fchorney/krakenpad-poc/review/01-master/02-2d-top.png

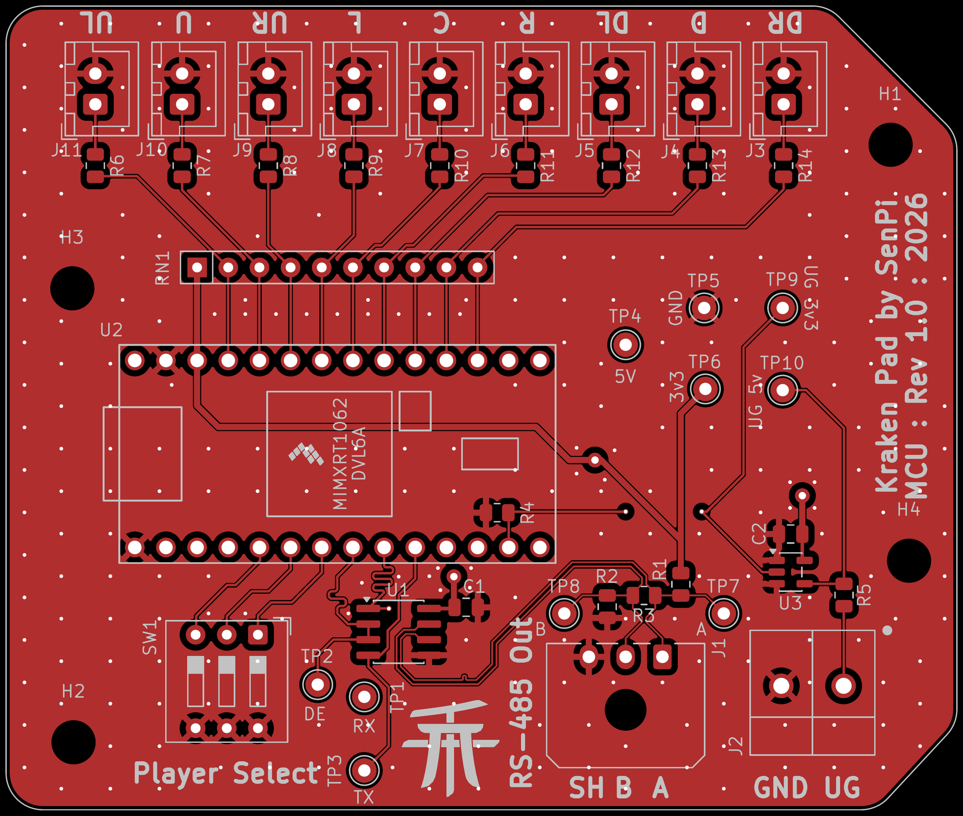
review/01-master/02-2d-top.png
