fchorney/krakenpad-poc/review/01-master/03-2d-in1.png

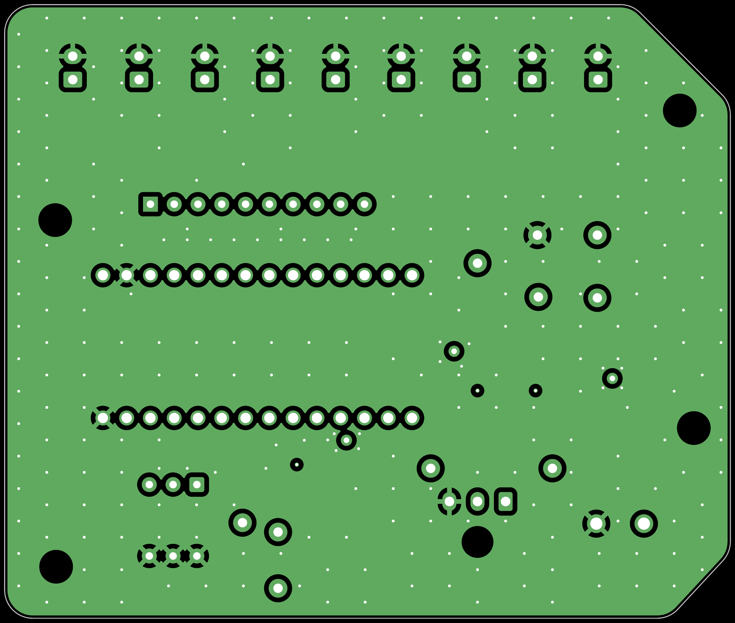
review/01-master/03-2d-in1.png
