fchorney/krakenpad-poc/review/01-master/05-2d-bottom-mirrored.png

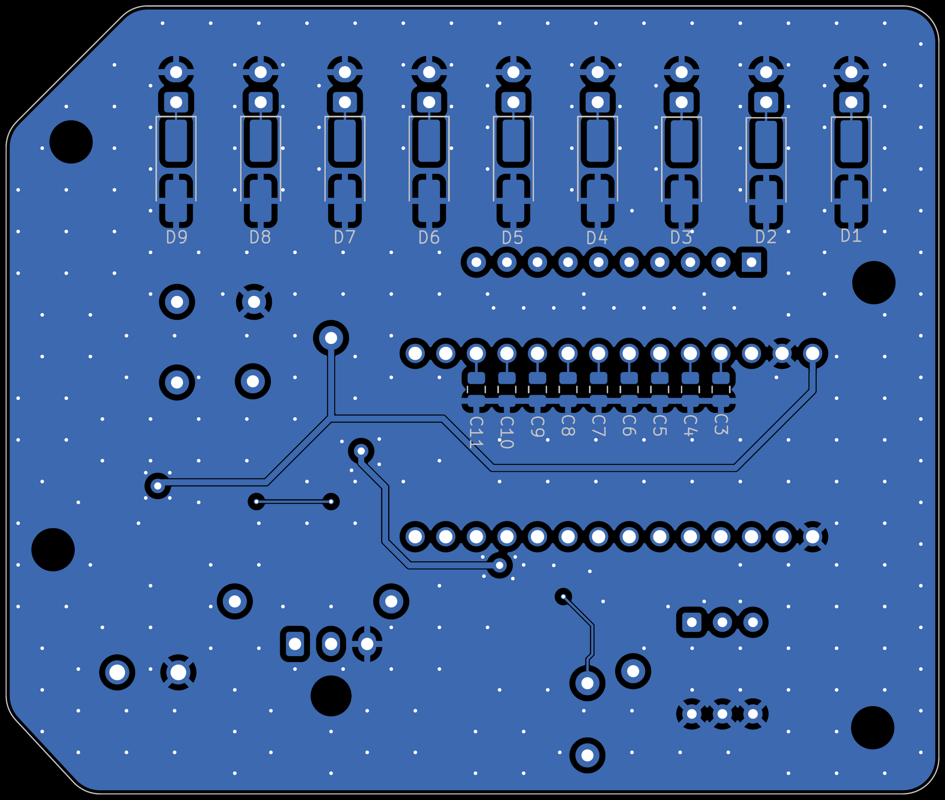
review/01-master/05-2d-bottom-mirrored.png
