fchorney/krakenpad-poc/review/01-master/06-2d-silkscreen-top.png

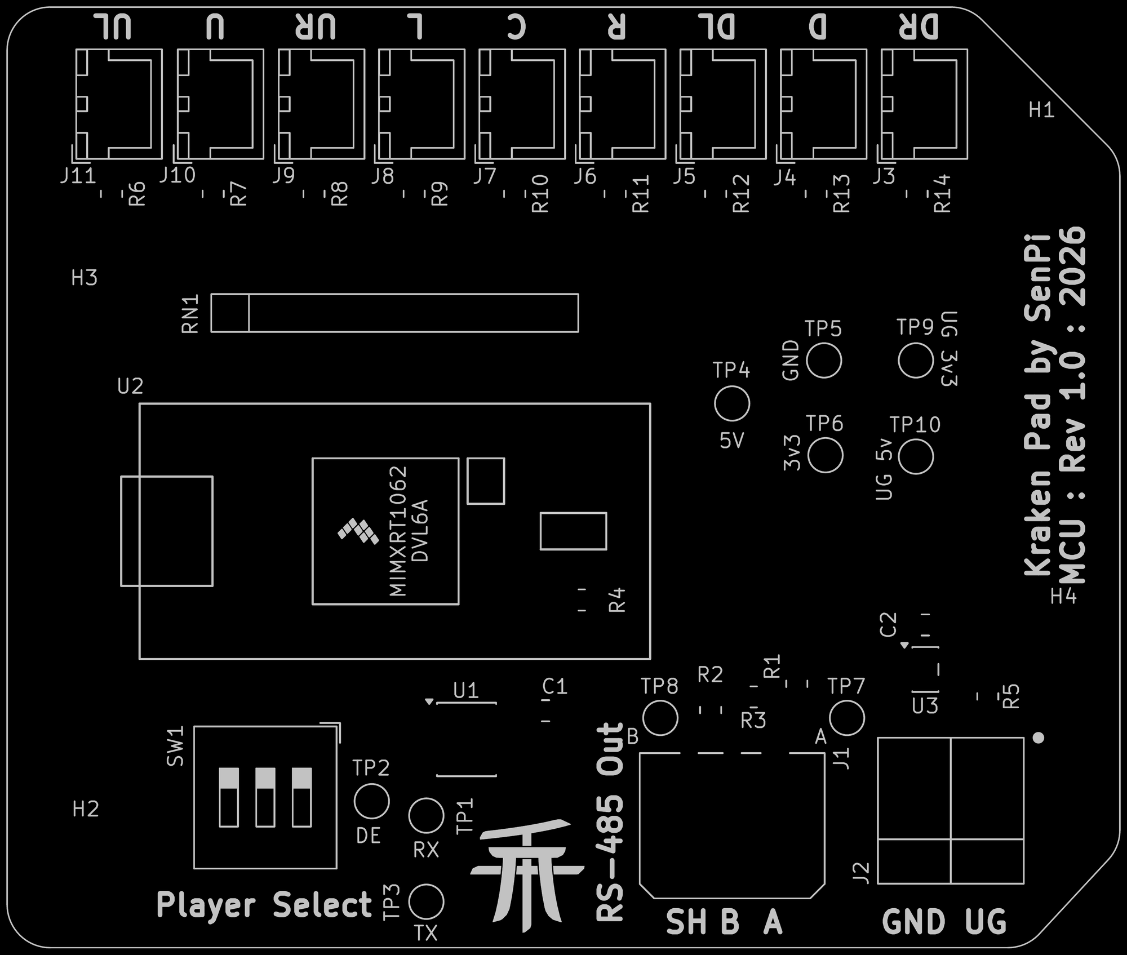
review/01-master/06-2d-silkscreen-top.png
