fchorney/krakenpad-poc/review/01-master/07-2d-top-no-pour.png

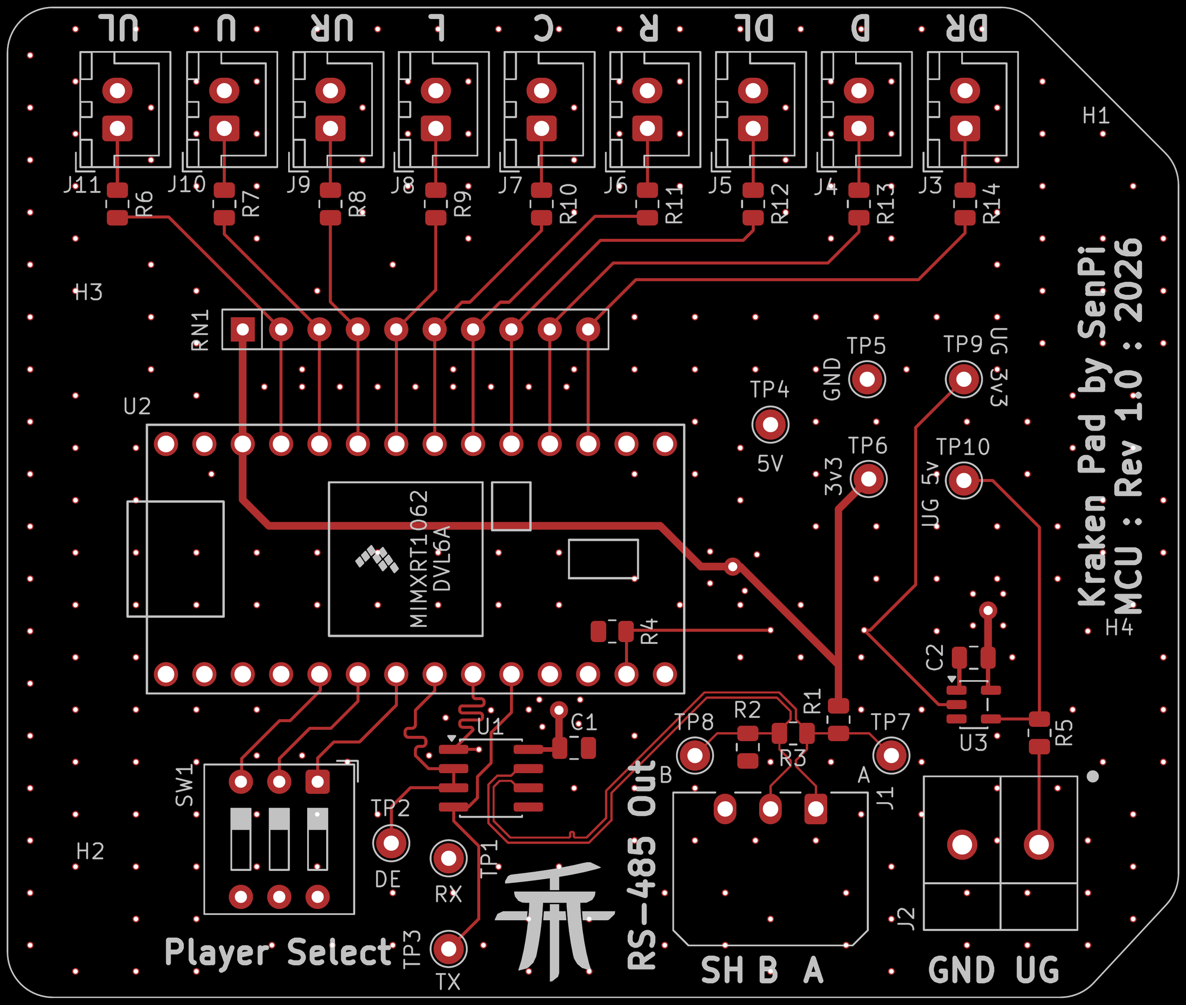
review/01-master/07-2d-top-no-pour.png
