fchorney/krakenpad-poc/review/01-master/08-2d-in1-no-pour.png

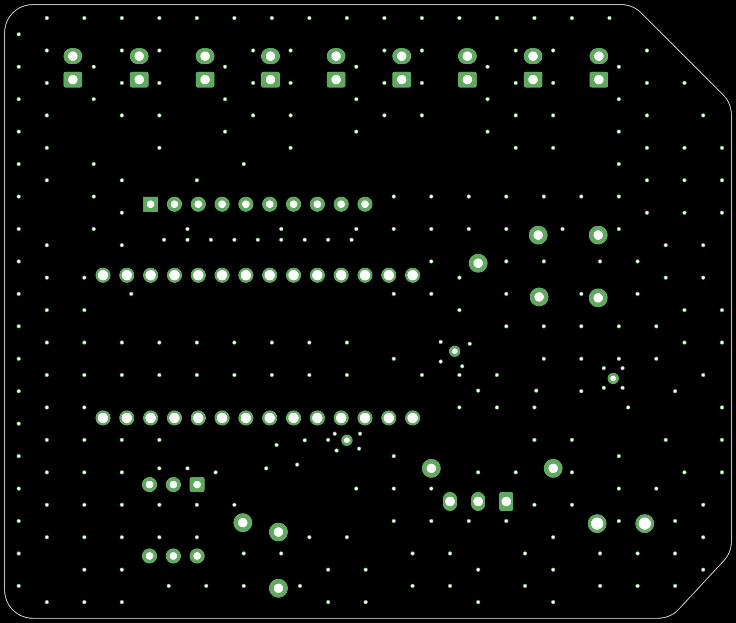
review/01-master/08-2d-in1-no-pour.png
