fchorney/krakenpad-poc/review/01-master/10-2d-bottom-no-pour-mirrored.png

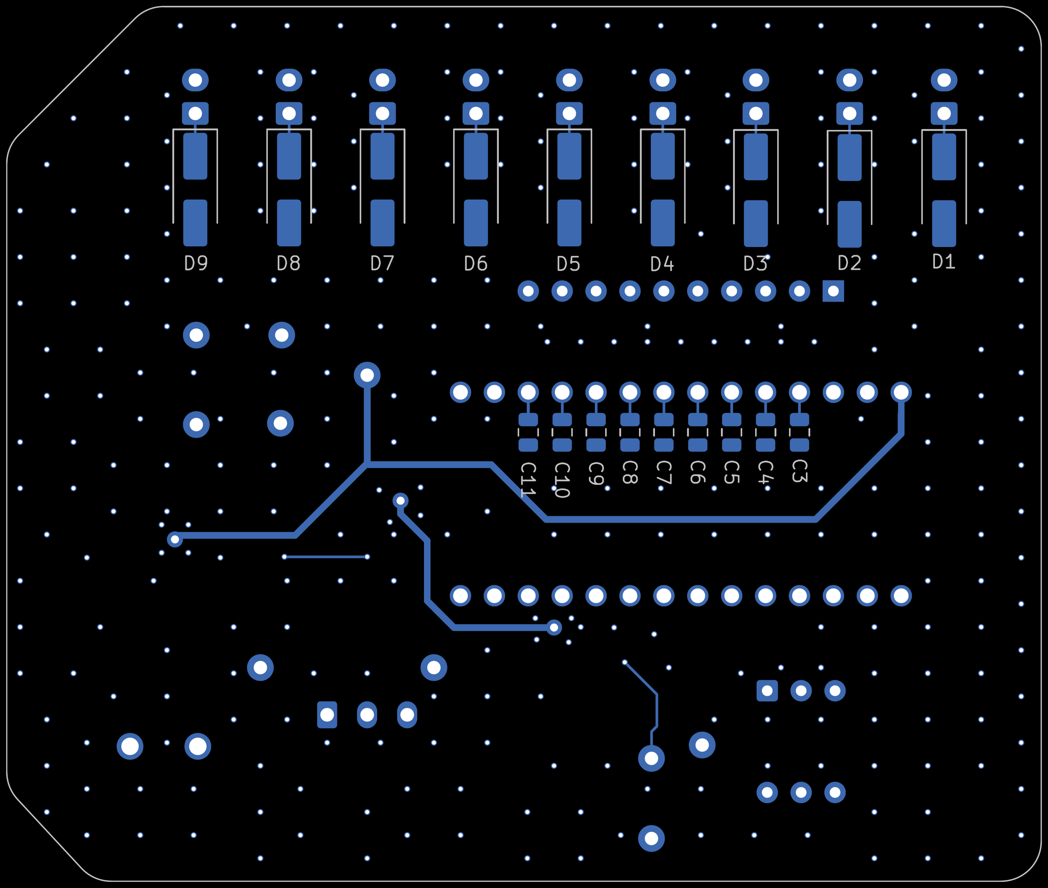
review/01-master/10-2d-bottom-no-pour-mirrored.png
