fchorney/krakenpad-poc/review/01-master/12-3d-bottom.png

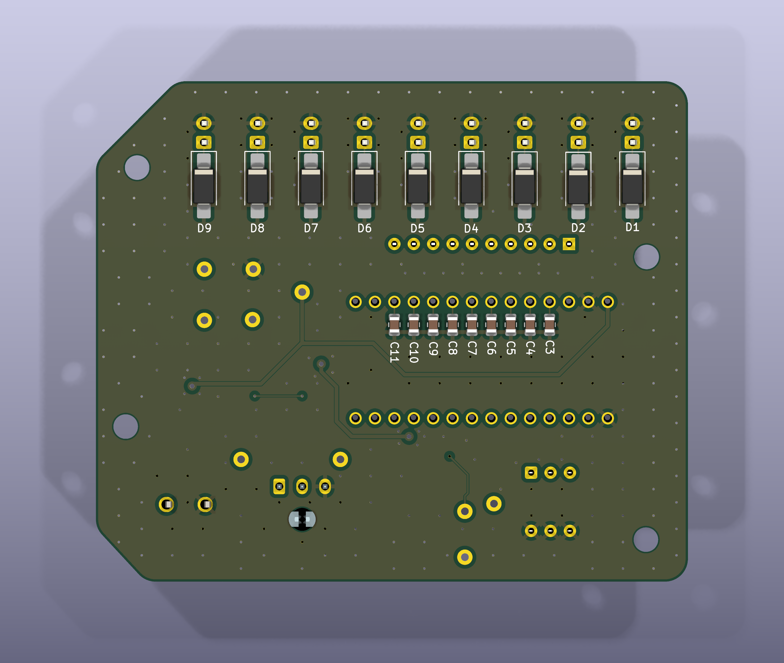
review/01-master/12-3d-bottom.png
