fchorney/krakenpad-poc/review/03-dual-carrier/02-2d-top.png

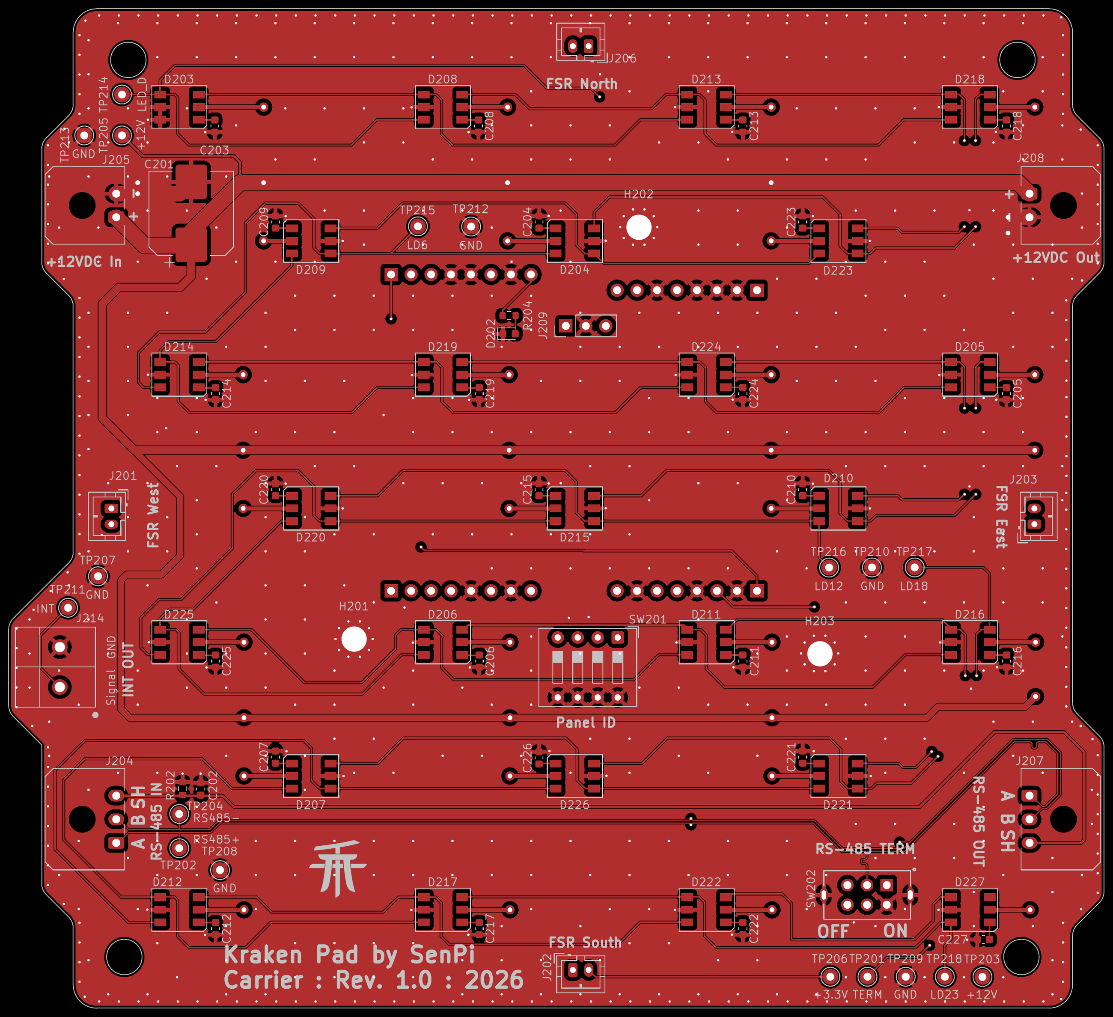
review/03-dual-carrier/02-2d-top.png
