fchorney/krakenpad-poc/review/03-dual-carrier/03-2d-in1.png

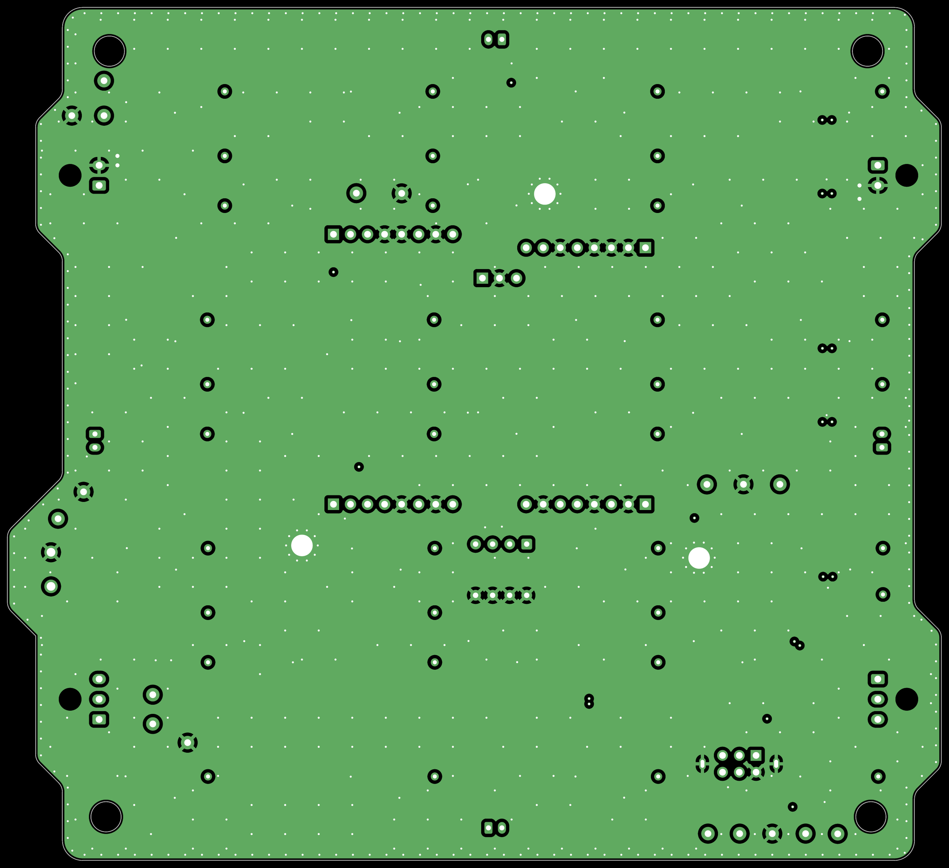
review/03-dual-carrier/03-2d-in1.png
