fchorney/krakenpad-poc/review/03-dual-carrier/05-2d-bottom-mirrored.png

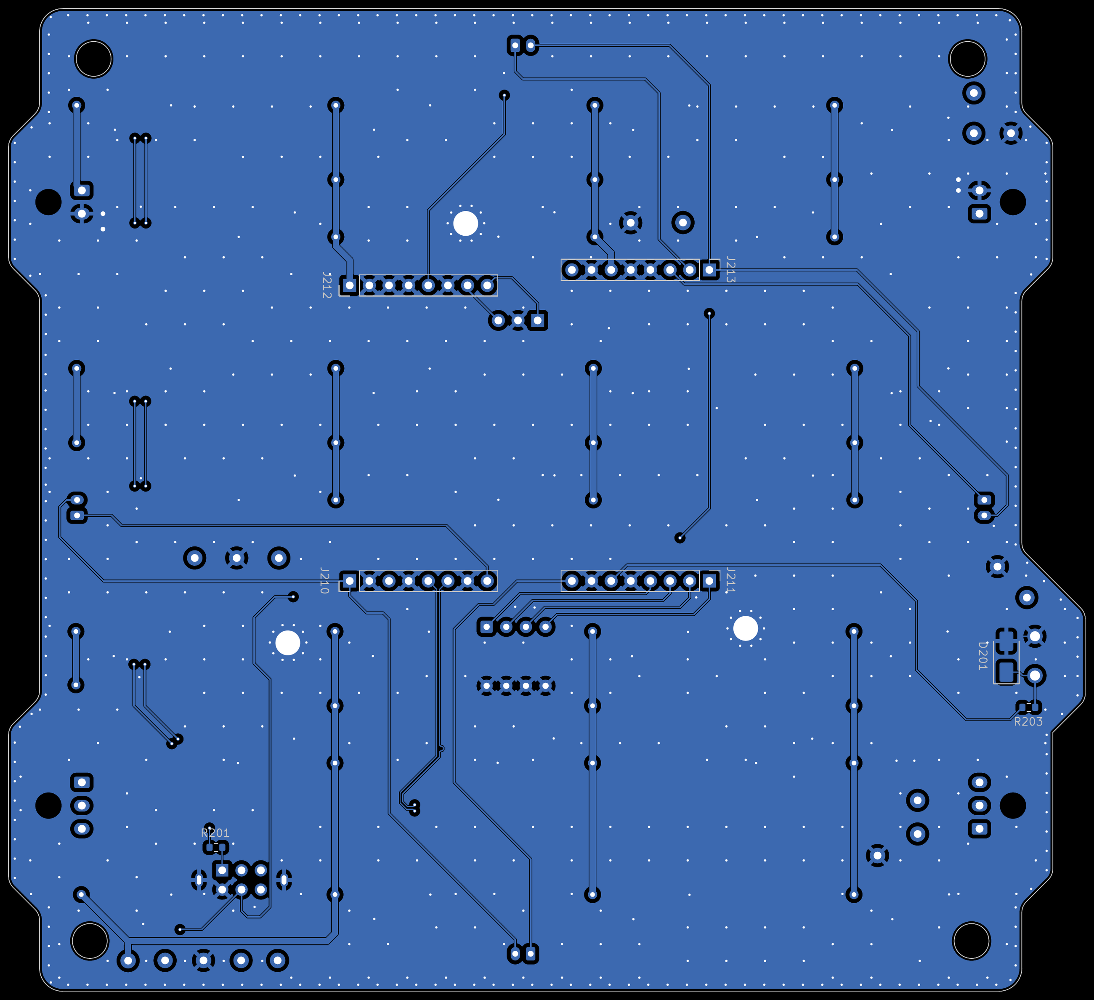
review/03-dual-carrier/05-2d-bottom-mirrored.png
