fchorney/krakenpad-poc/review/03-dual-carrier/06-2d-silkscreen-top.png

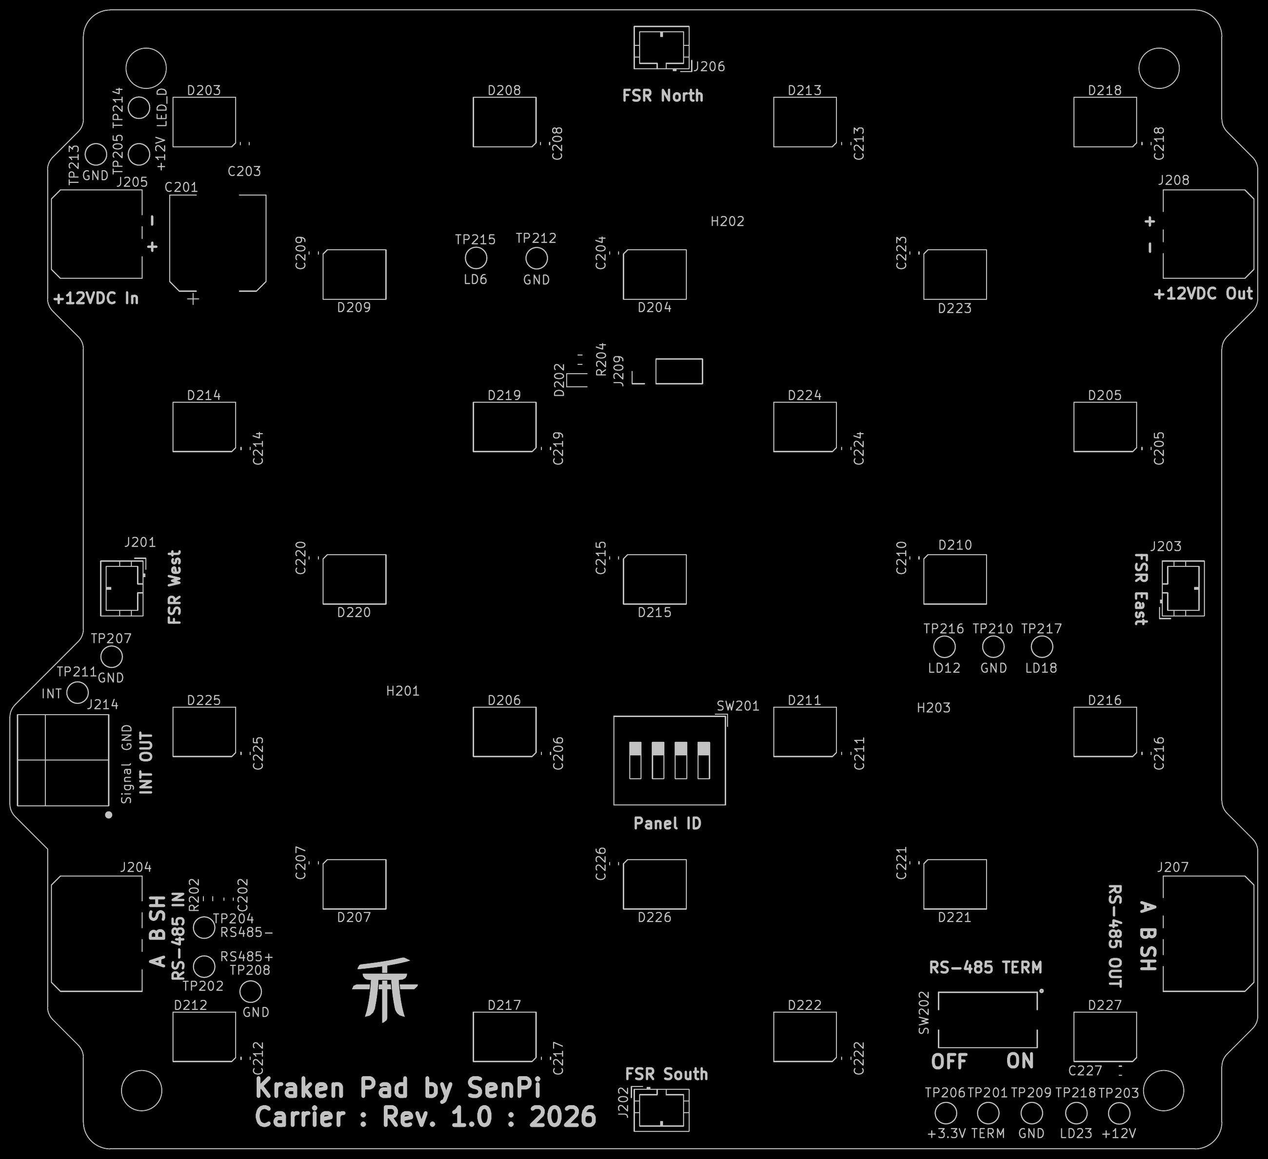
review/03-dual-carrier/06-2d-silkscreen-top.png
