fchorney/krakenpad-poc/review/03-dual-carrier/07-2d-top-no-pour.png

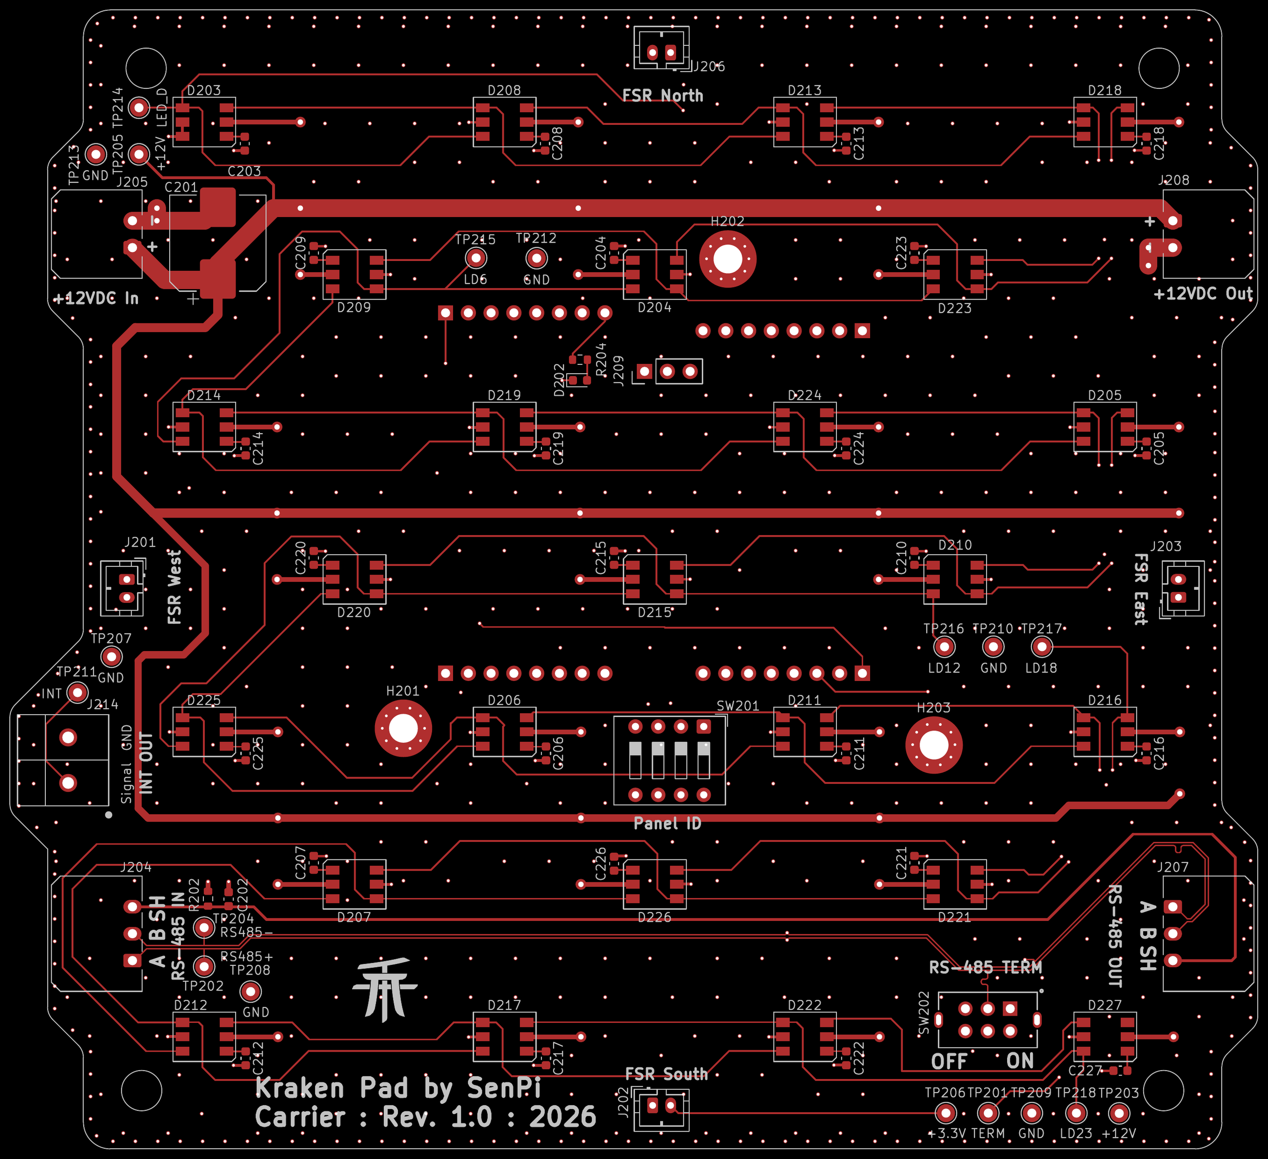
review/03-dual-carrier/07-2d-top-no-pour.png
