fchorney/krakenpad-poc/review/03-dual-carrier/08-2d-in1-no-pour.png

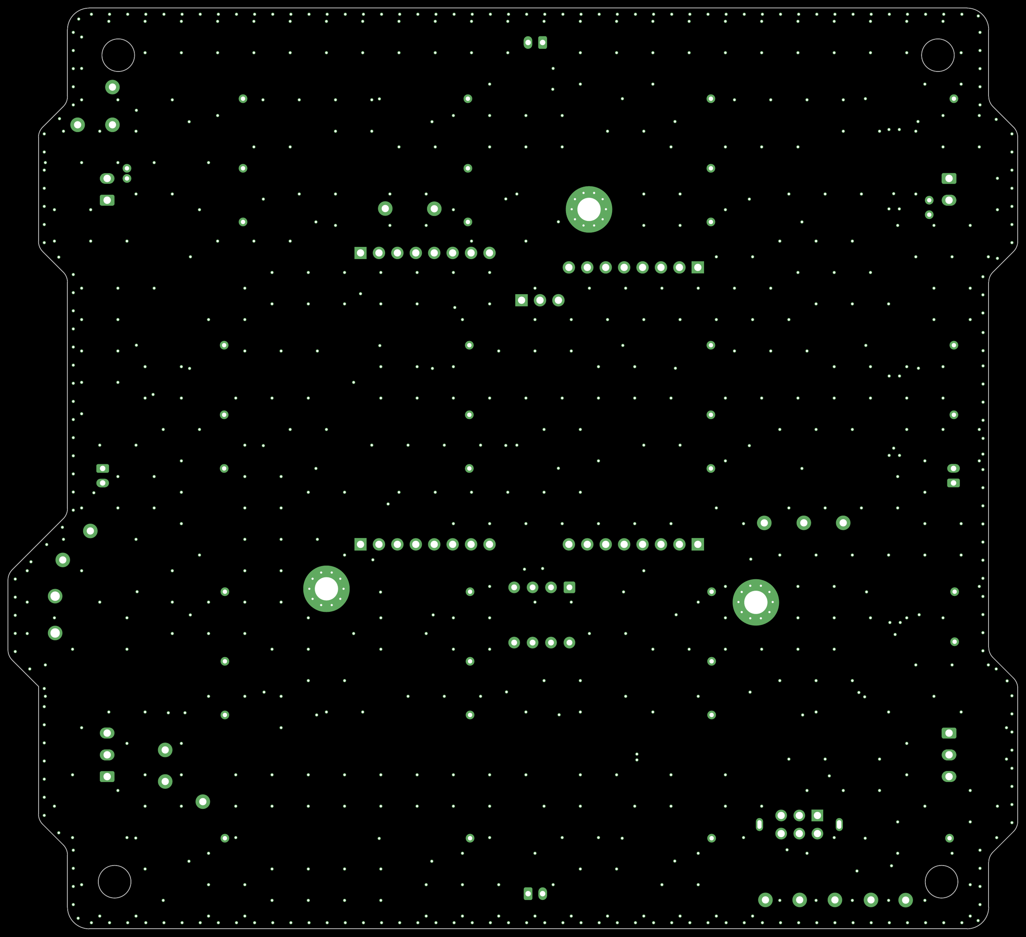
review/03-dual-carrier/08-2d-in1-no-pour.png
