fchorney/krakenpad-poc/review/03-dual-carrier/10-2d-bottom-no-pour-mirrored.png

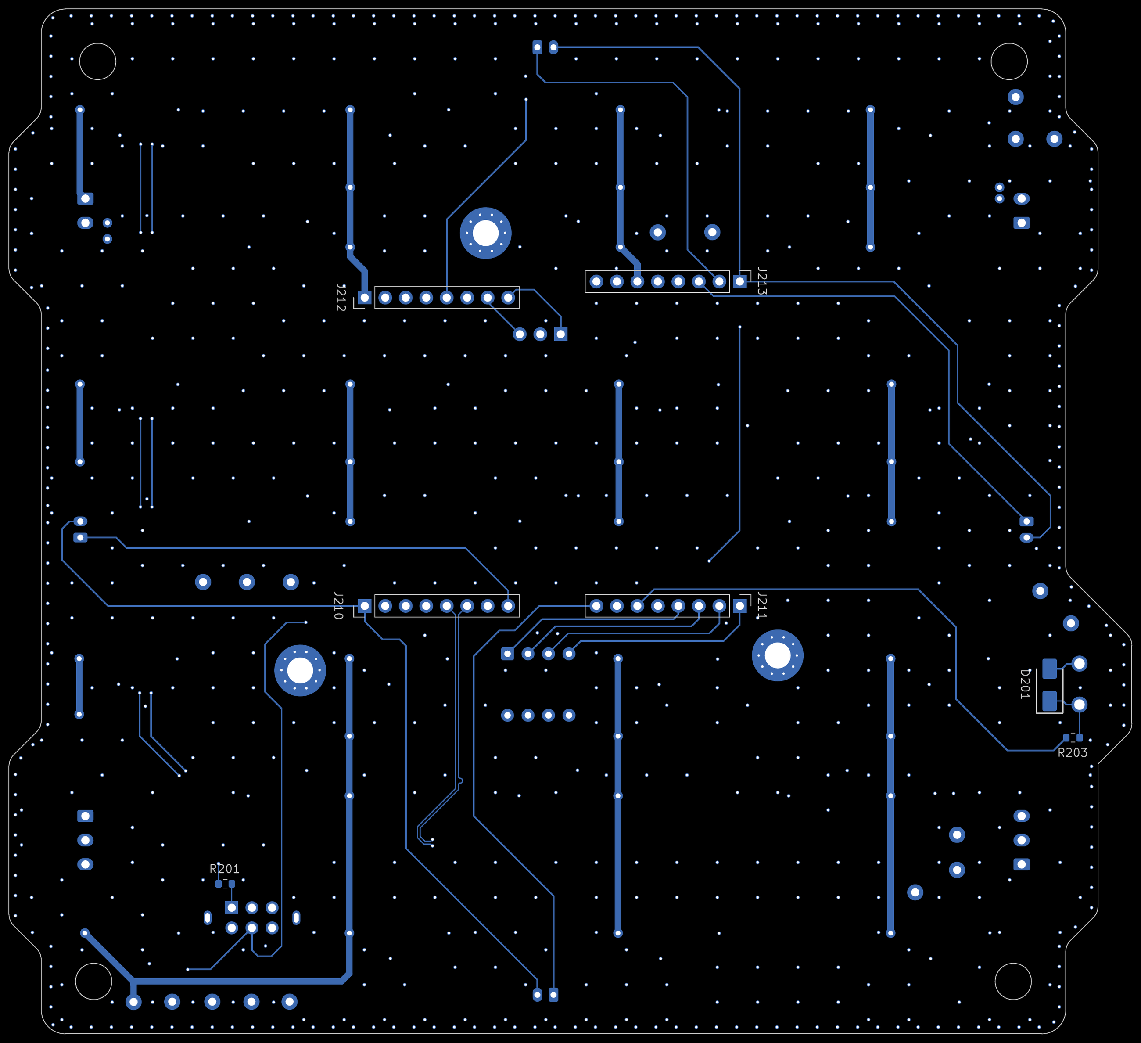
review/03-dual-carrier/10-2d-bottom-no-pour-mirrored.png
