fchorney/krakenpad-poc/review/03-dual-carrier/11-3d-top.png

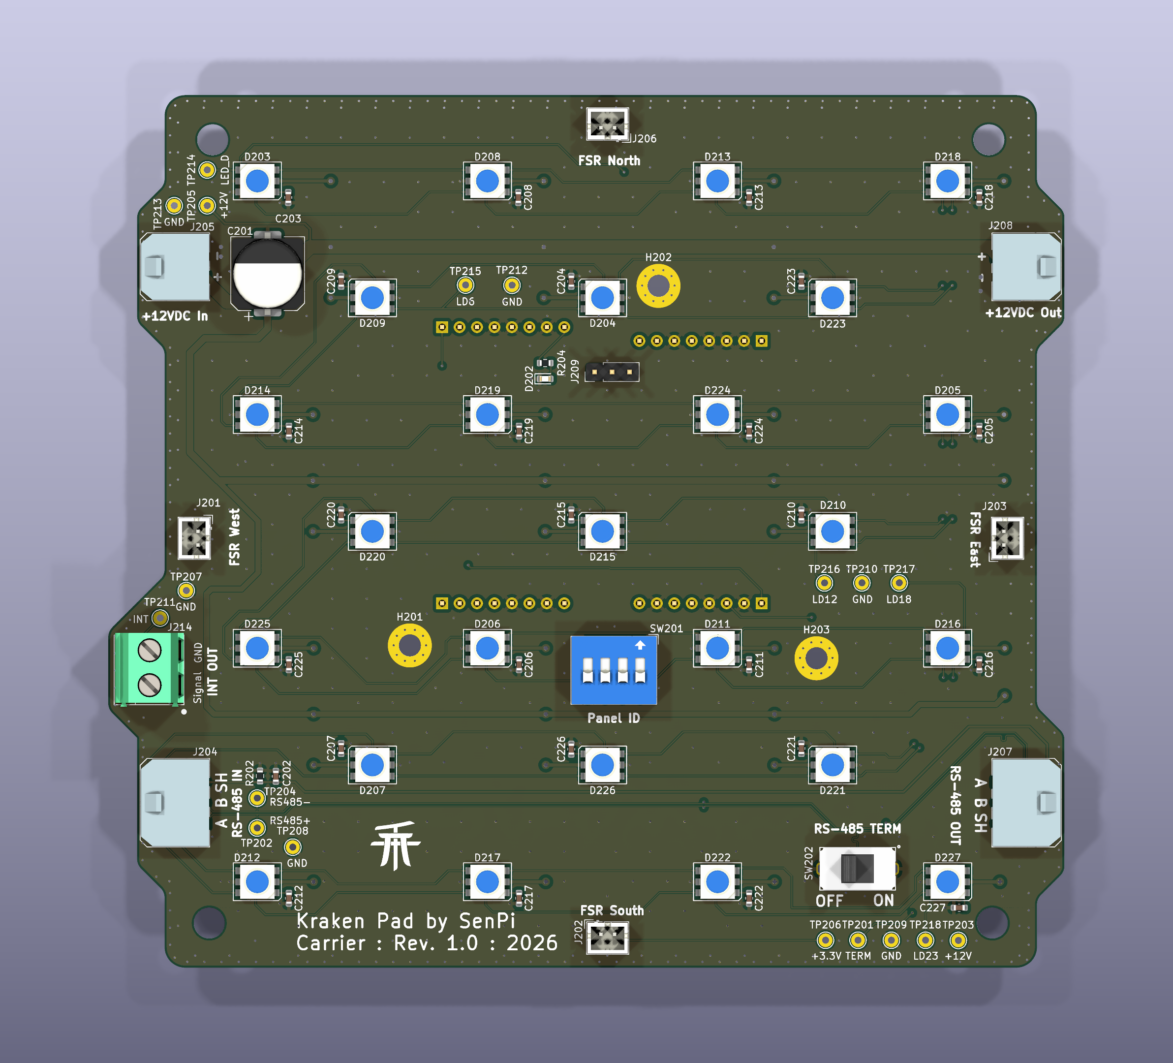
review/03-dual-carrier/11-3d-top.png
