fchorney/krakenpad-poc/review/03-dual-carrier/12-3d-bottom.png

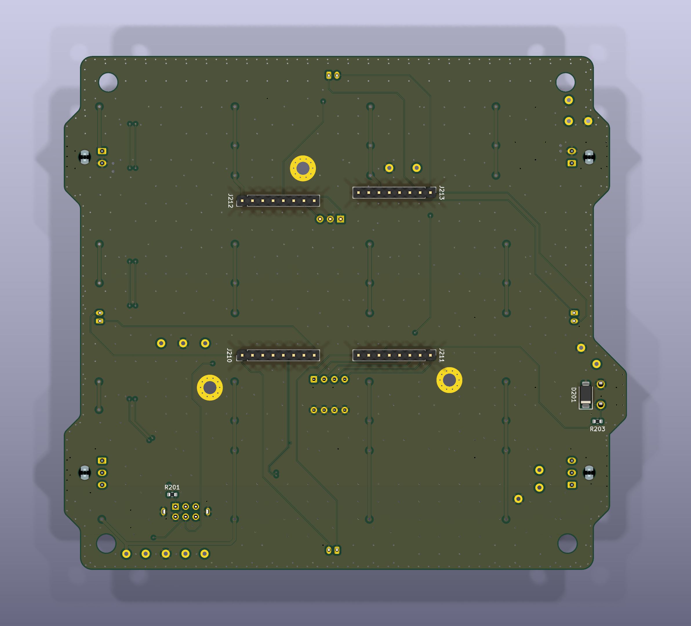
review/03-dual-carrier/12-3d-bottom.png
