fchorney/krakenpad-poc/review/04-dual-brain/02-2d-top.png

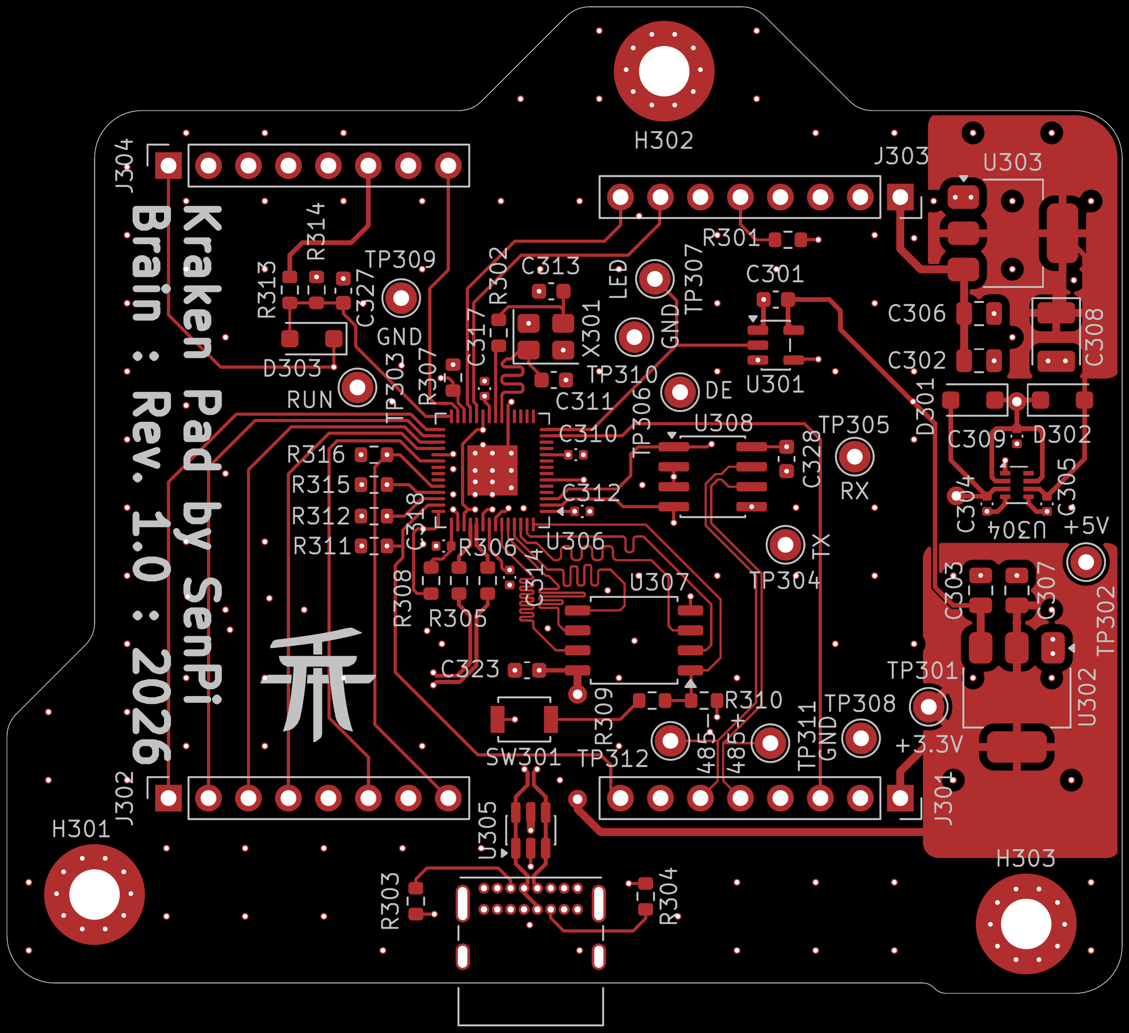
review/04-dual-brain/02-2d-top.png
