fchorney/krakenpad-poc/review/04-dual-brain/03-2d-in1.png

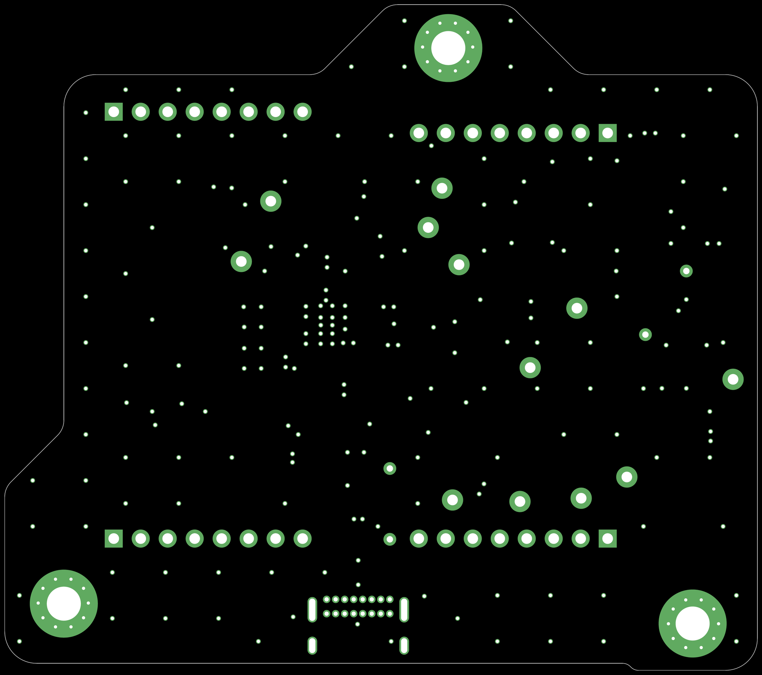
review/04-dual-brain/03-2d-in1.png
