fchorney/krakenpad-poc/review/04-dual-brain/05-2d-bottom-mirrored.png

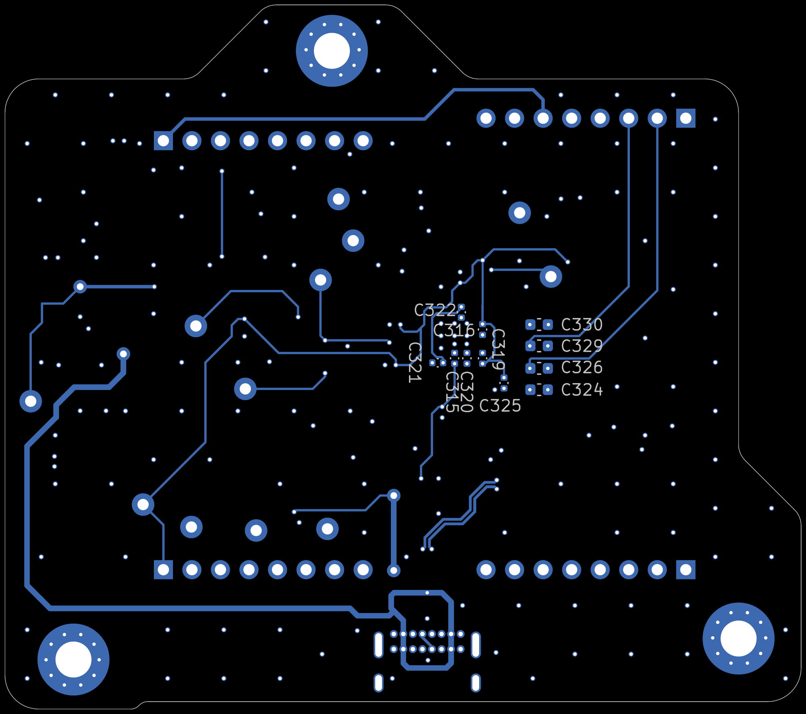
review/04-dual-brain/05-2d-bottom-mirrored.png
