fchorney/krakenpad-poc/review/04-dual-brain/06-2d-silkscreen-top.png

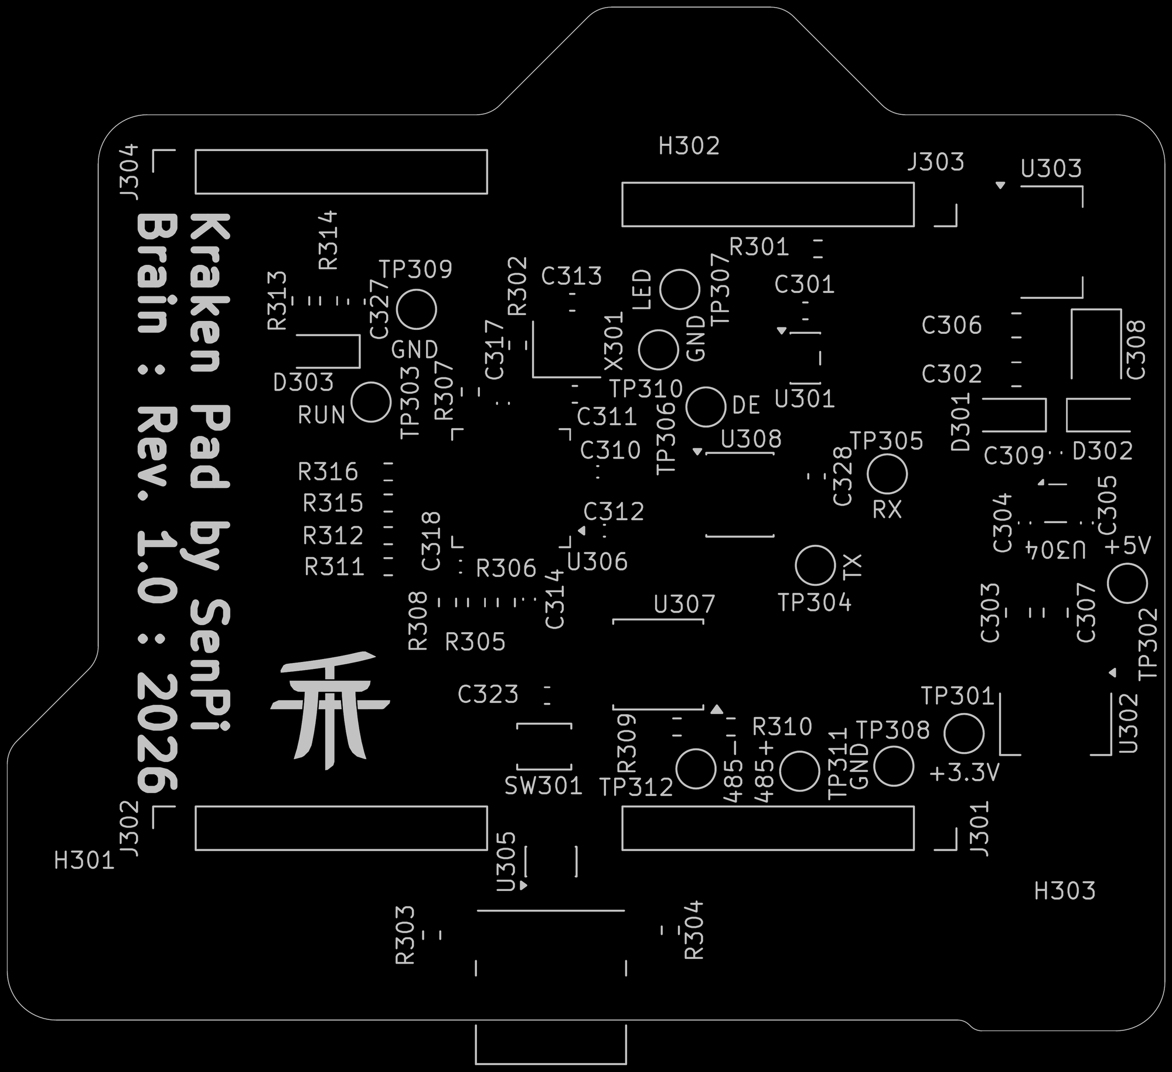
review/04-dual-brain/06-2d-silkscreen-top.png
