fchorney/krakenpad-poc/review/04-dual-brain/07-2d-top-no-pour.png

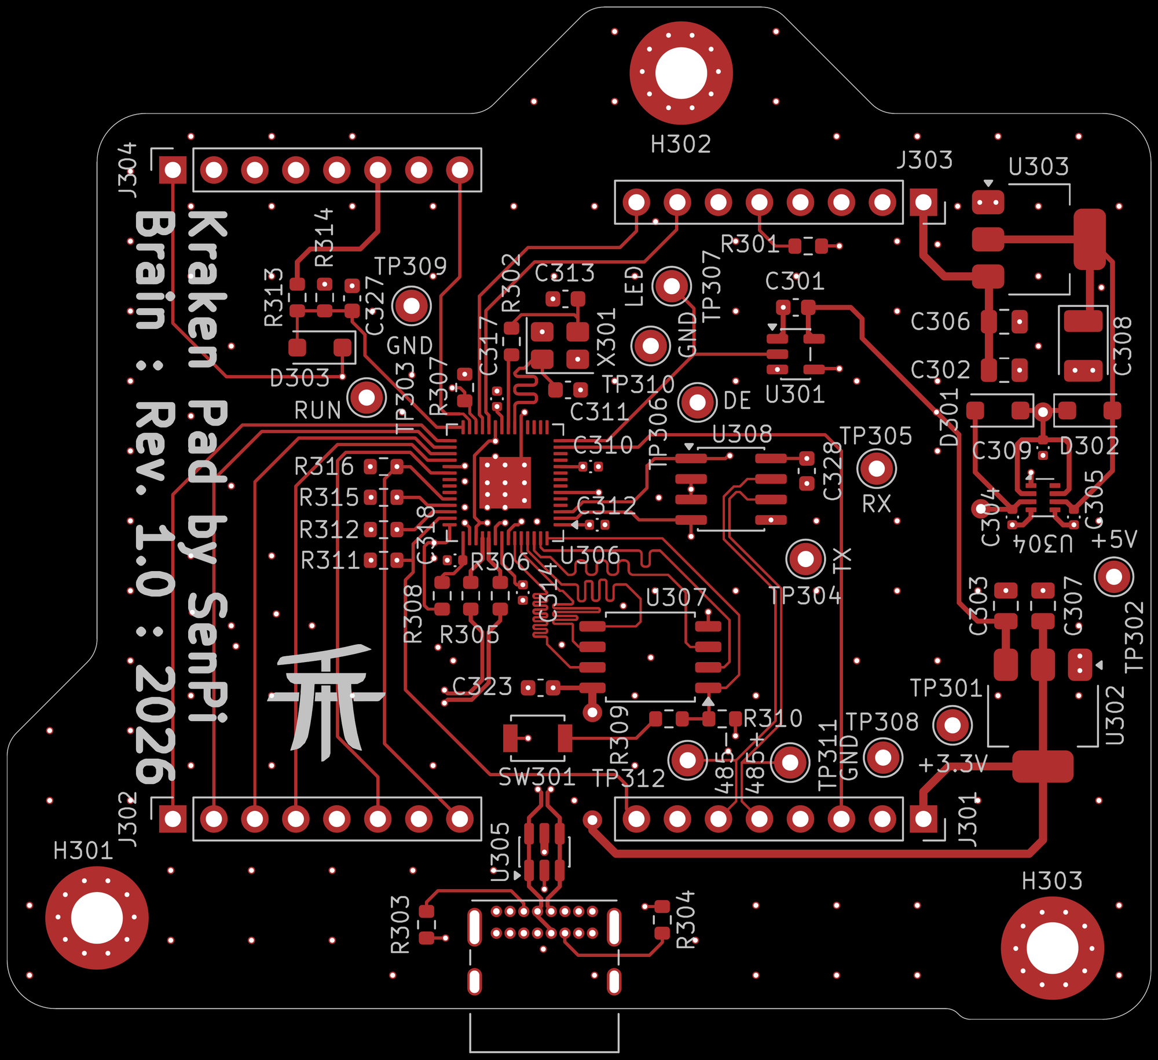
review/04-dual-brain/07-2d-top-no-pour.png
