fchorney/krakenpad-poc/review/04-dual-brain/12-3d-bottom.png

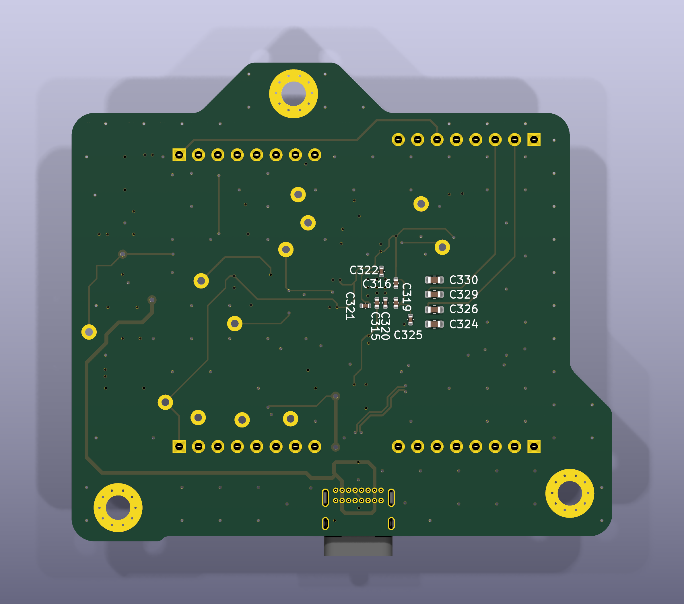
review/04-dual-brain/12-3d-bottom.png
