fchorney/krakenpad-poc/stock-smx/harness/psu-12v.yml

metadata:
  title: 12V PSU and its output harness
  description: >
    Picks up where ac-input.yml ends. The locking C13 plugs into the C14 inlet
    of a 102 W 12 V switching supply (model YU1208), whose output cable runs
    through a 5.5x2.5 DC BARREL PAIR (identified 2026-08-16 by removing the
    heatshrink -- it was recorded as an unidentified joint until then) to a
    JST YL 2-way connector carrying 12 V and GND into the rest of the pad.
    Recorded at the 2026-08-08 teardown. STOCK wiring, documented not redesigned.
    Nameplate capacity is DC 12 V 8.5 A. Whether that is enough for THIS
    project, and whether the supply is kept, are design questions and live in
    the hardware/harness tree (README.md "Power budget", 12v-trunk.yml) -- not here.
  status: STOCK -- as found at the 2026-08-08 teardown. Descriptive only.
  pn: HARNESS-PWR12-01
  qty_per_pad: 1

options:
  color_mode: full

connectors:
  AC_OUT:
    pn: XUANHUA XC13-X
    type: IEC 60320 C13 connector, female
    subtype: locking, 13 A 250 V
    pincount: 3
    pinlabels: [L, N, GND]
    notes: >
      Shown for context only -- this is the far end of ac-input.yml, repeated
      here so the handoff between the two drawings is visible. The arrow is a
      mating, not a cable.

  PSU_IN:
    pn: YU1208
    type: 12V switching PSU, AC inlet side
    subtype: IEC 60320 C14 inlet
    pincount: 3
    pinlabels: [L, N, GND]
    notes: >
      Mates the locking C13 at the end of ac-input.yml. Mounted immediately
      45 cm from the EMI filter along the mains cable.
      Nameplate, read directly off the back of the supply at teardown:
      102 W, model YU1208.
      INPUT  AC 100-240 V, 1.8 A, 50-60 Hz.
      OUTPUT DC 12 V, 8.5 A.
      Polarity marking: OUTER = NEGATIVE, INNER = POSITIVE.

  PSU_OUT:
    pn: YU1208
    type: 12V switching PSU, DC output side
    subtype: DC 12 V, 8.5 A
    pincount: 2
    pinlabels: [V12, GND]
    notes: >
      PSU_IN and PSU_OUT are the two sides of ONE physical supply, drawn
      separately because WireViz models a connector as a single pin set.
      Nameplate, as found: DC 12 V, 8.5 A, 102 W, model YU1208.
      The pad is believed to be a Gen 5, but CLAUDE.md records Gen 5 as
      12 V 15 A, which this is not. Either the manual figure is wrong or these
      pads shipped with a different supply. UNRESOLVED, and recorded as an
      observation only.
      Whether this supply is kept or replaced is a DESIGN question, not a stock
      one -- see the hardware/harness tree (README.md "Power budget", 12v-trunk.yml). Earlier revisions
      of this file carried that debate plus three superseded current figures
      (8.1 A, 11.2 A, 13.8 A); all of it has been moved out.

  JOINT:
    type: Inline DC barrel connector pair
    subtype: 5.5 mm OD / 2.5 mm ID -- CONFIRMED 2026-08-16
    pincount: 2
    pinlabels: [V12, GND]
    notes: >
      IDENTIFIED 2026-08-16 by removing the heatshrink: it is a standard
      5.5x2.5 DC BARREL PAIR joining the PSU's own 18 AWG output cable to the
      20 AWG tail -- not a splice. Measured: barrel end 5.5 mm OD with a 2.5 mm
      ID bore; mating half 5.5 mm ID with a 2.5 mm centre pin.
      THE PRE-TEARDOWN INFERENCE WAS RIGHT. This file already reasoned it was
      "most likely a barrel plug and socket pair, since the supply is labelled
      with barrel polarity and brick supplies of this type normally terminate
      in one", and flagged it as inference rather than observation. It is now
      observation. Recording the hit because the same reasoning -- read the
      supply's own label, then trust the convention -- is worth reusing.
      POLARITY: the supply's label reads outer negative, inner positive, i.e.
      CENTRE-POSITIVE, the usual convention. Still worth a meter check before
      connecting anything, but there is no longer any mystery here.
      THE SUPPLY CARRIES THE PLUG, the tail the receptacle -- confirmed
      2026-08-16, matching convention.
      This barrel is the ONLY unambiguous polarity reference on the supply side,
      because both conductors of W_PSU_OUT are black and the moulded ridge's
      meaning is not recorded anywhere. That is a property of the stock pad and
      is why it matters to anyone working on it.
      What our own harness does with this connector is a DESIGN question --
      see 12v-trunk.yml.

  YL2:
    pn: JST YLR-02V
    type: JST YL 2-way receptacle
    subtype: YLR-02V, receptacle (pin contacts)
    pincount: 2
    pinlabels: [GND, V12]
    notes: >
      THE COLORS ARE THE RELIABLE RECORD: RED = 12 V, BLACK = GND.
      PIN 1 = GND (BLACK), PIN 2 = 12 V (RED) -- re-read off the part
      2026-08-08. This REVERSES the earlier reading, which had 12 V on pin 1;
      that one was derived under the wrong gender call, not observed.
      GENDER RESOLVED 2026-08-08: this is the RECEPTACLE, carrying MALE PIN
      contacts (SYM). It was recorded as a YLP-02V, which was backwards -- see
      PARTS.md, "Connector gender conventions", for why JST's receptacle is the
      male half. Its mate at the star point is the plug (YLP_A in
      12v-distribution.yml).
      The pin numbering here was DERIVED under the old, wrong gender reading,
      and receptacle and plug housings number as mirror images -- so pins 1 and
      2 may need to swap. With only two contacts and unambiguous red/black wire
      colors, nothing electrical depends on it. WIRE BY COLOR.
      These housings carry NO moulded position numbers -- checked 2026-08-08 --
      so an absolute pin number cannot be observed on the part at all, only
      derived. See MEASUREMENTS.md, "Pinout re-verification pass": position is
      recorded against the LATCH instead, which needs no vendor convention.

cables:
  W_PSU_OUT:
    category: bundle
    gauge: 18 AWG
    length: 1.0
    colors: [BK, BK]
    notes: >
      The supply's own captive output cable, 2-conductor 18 AWG. LONG, and
      stored bunched up and twist-tied inside the pad -- the length is not
      load-bearing and was deliberately not measured. 1.0 m here is a
      placeholder for drawing purposes only.
      BOTH CONDUCTORS ARE BLACK. One of them carries a moulded RIDGE down the
      jacket; that ridge is the only way to tell them apart, and WireViz cannot
      draw it, so both wires render identically here. Read the note, not the
      picture.
      WHICH ONE IS +12V IS NOT RECORDED. Do NOT assume the ridge marks positive
      -- the convention is not consistent across supplies, and getting it
      backwards reverses polarity into every panel. Resolve it with a meter:
      the tail on the far side of the joint is unambiguous (red = 12 V,
      black = GND), so a continuity check through the joint settles it, or just
      measure the supply's output directly with it powered.

  W_TAIL:
    category: bundle
    gauge: 20 AWG
    length: 0.300
    colors: [BK, RD]
    notes: >
      Jacketed 2-conductor, 30 cm, from the concealed joint to the YL 2-way.
      Colors CONFIRMED at teardown: RED = 12 V, BLACK = GND.
      Wire order follows the YL 2-way's pin order, which is GND first as of the
      2026-08-08 re-read -- hence black listed before red.

connections:
  - - AC_OUT: [1-3]
    - ==>
    - PSU_IN: [1-3]

  - - PSU_OUT: [1-2]
    - W_PSU_OUT: [1-2]
    - JOINT: [1-2]

  - - JOINT: [2]
    - W_TAIL: [1]
    - YL2: [1]
  - - JOINT: [1]
    - W_TAIL: [2]
    - YL2: [2]
